newtontriumphant/glockwork-orange/Assets/Cart-Screenshots/Amazon_Cart_3.png

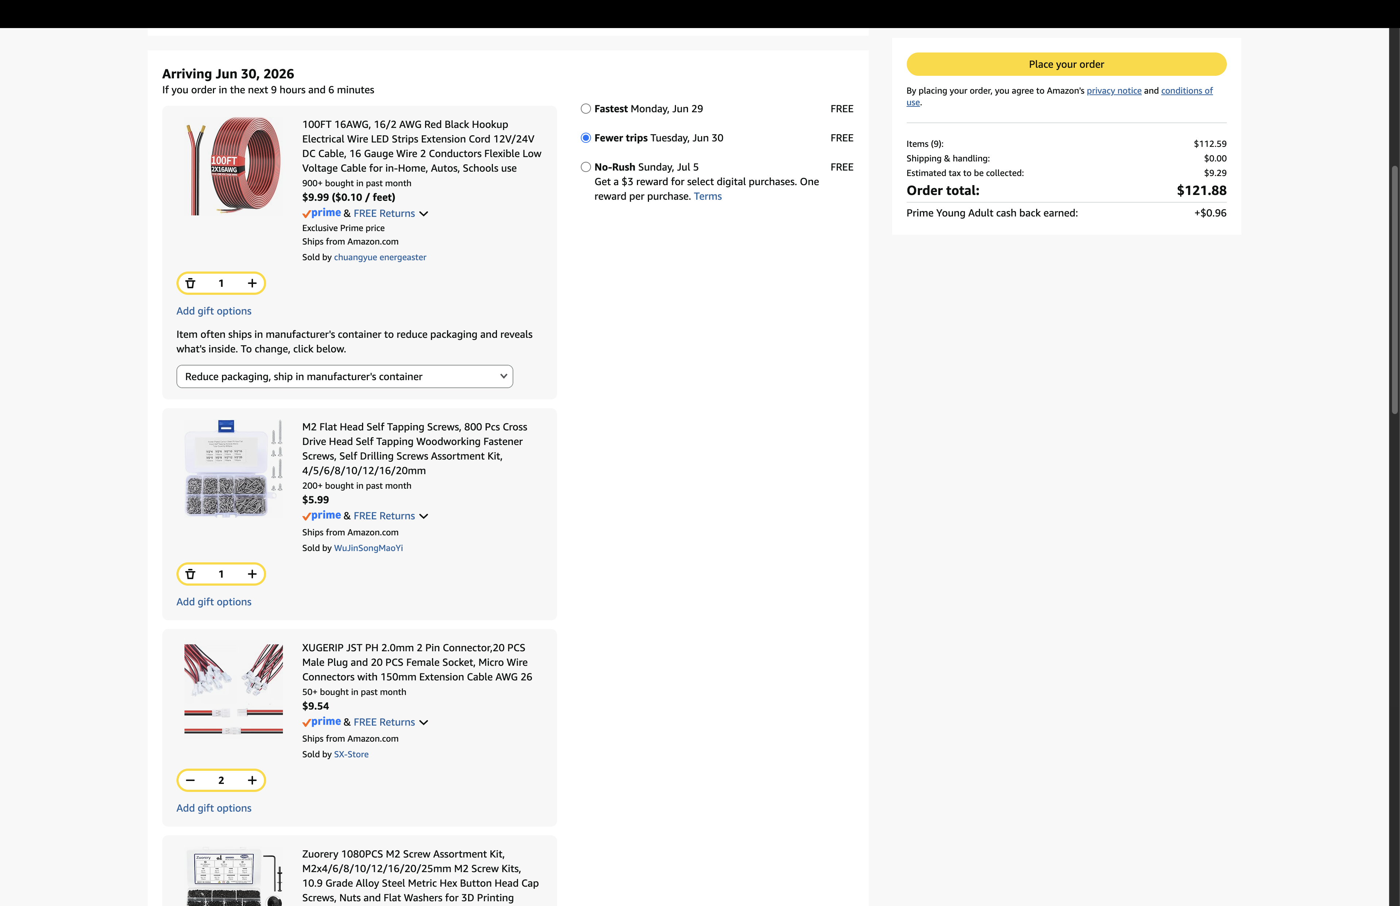
Assets/Cart-Screenshots/Amazon_Cart_3.png
