newtontriumphant/glockwork-orange/Assets/Cart-Screenshots/Digikey_Cart_2.png

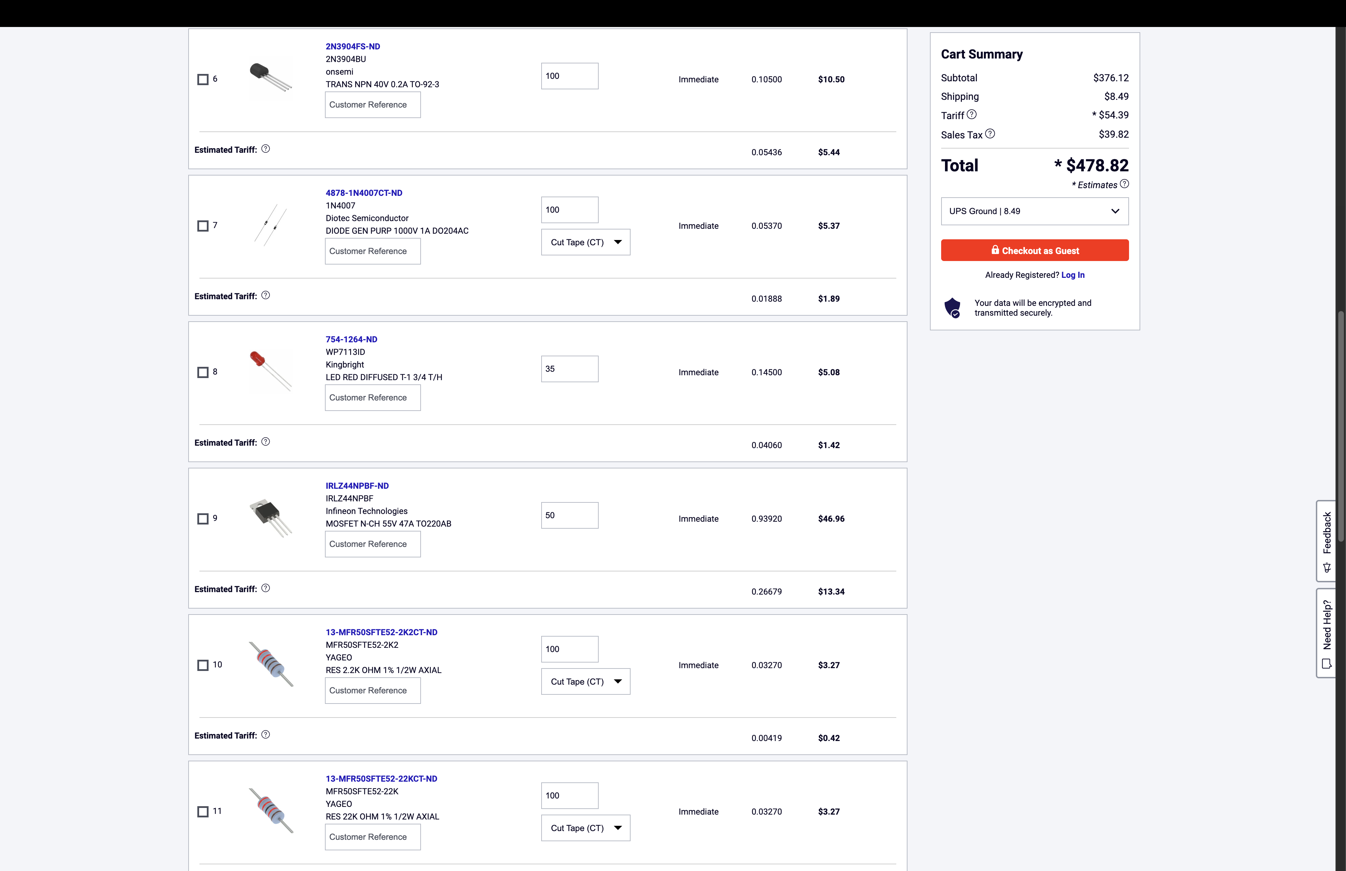
Assets/Cart-Screenshots/Digikey_Cart_2.png
