newtontriumphant/glockwork-orange/Assets/Cart-Screenshots/Digikey_Cart_Final.png

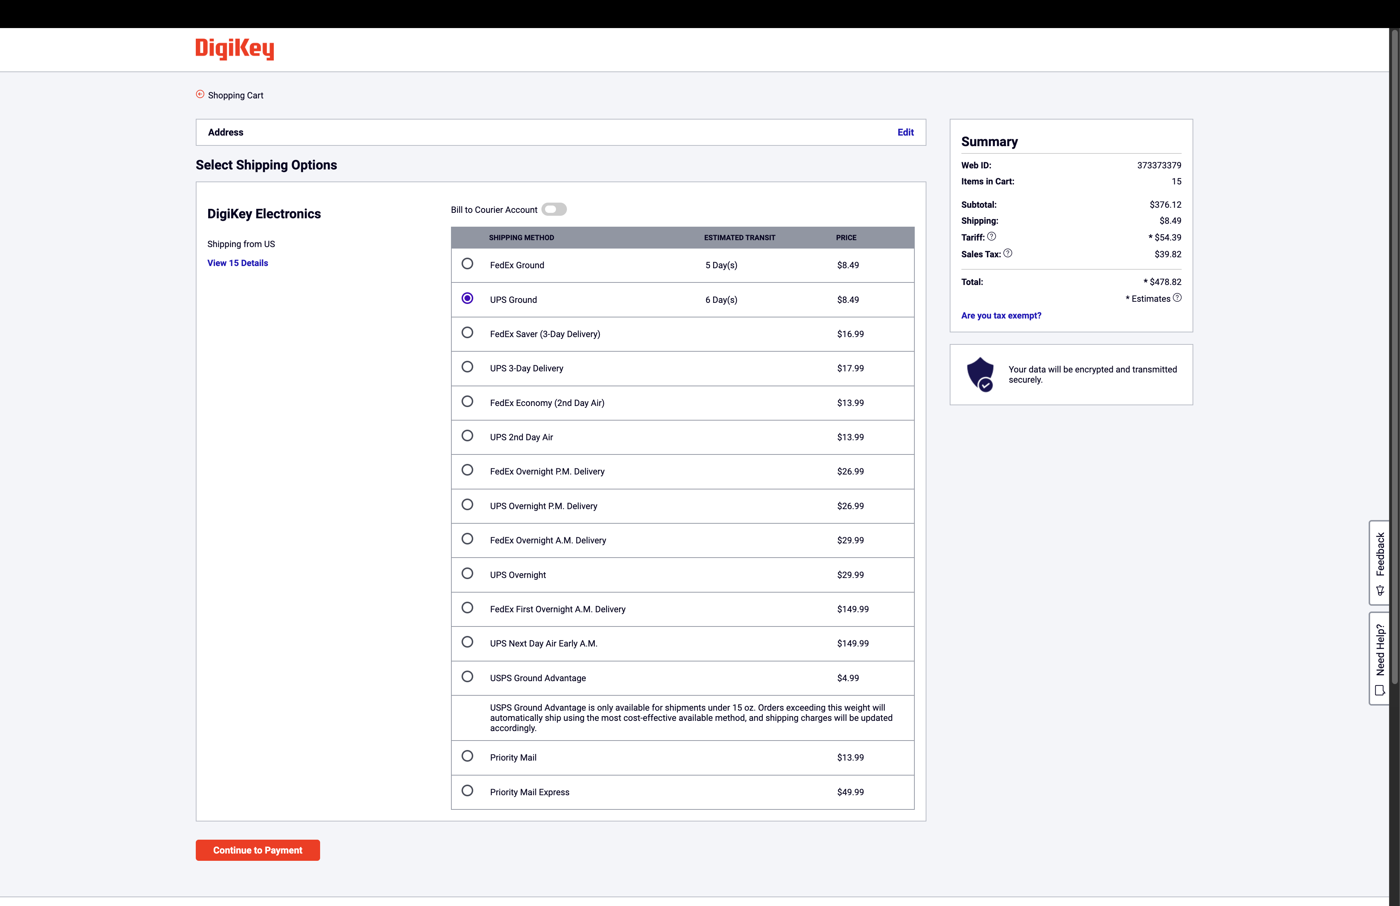
Assets/Cart-Screenshots/Digikey_Cart_Final.png
