newtontriumphant/glockwork-orange/Assets/Cart-Screenshots/JLC_Cart_2.png

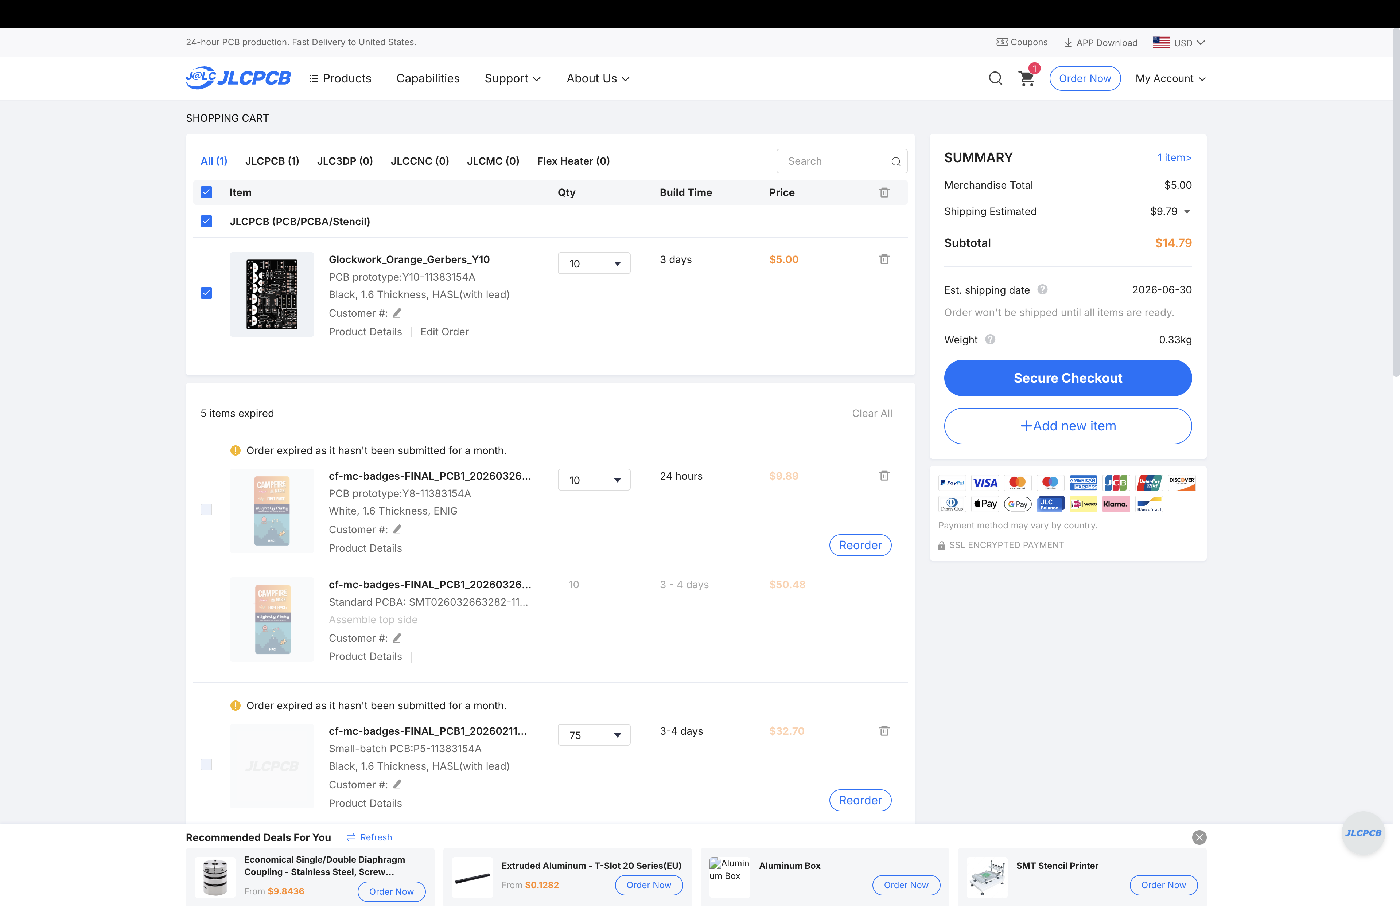
Assets/Cart-Screenshots/JLC_Cart_2.png
